antmicro/modular-agilex5e-dc-scm/bios.kicad_sch

## KiCad design bios.kicad_sch (2026-10-01, an earlier design)

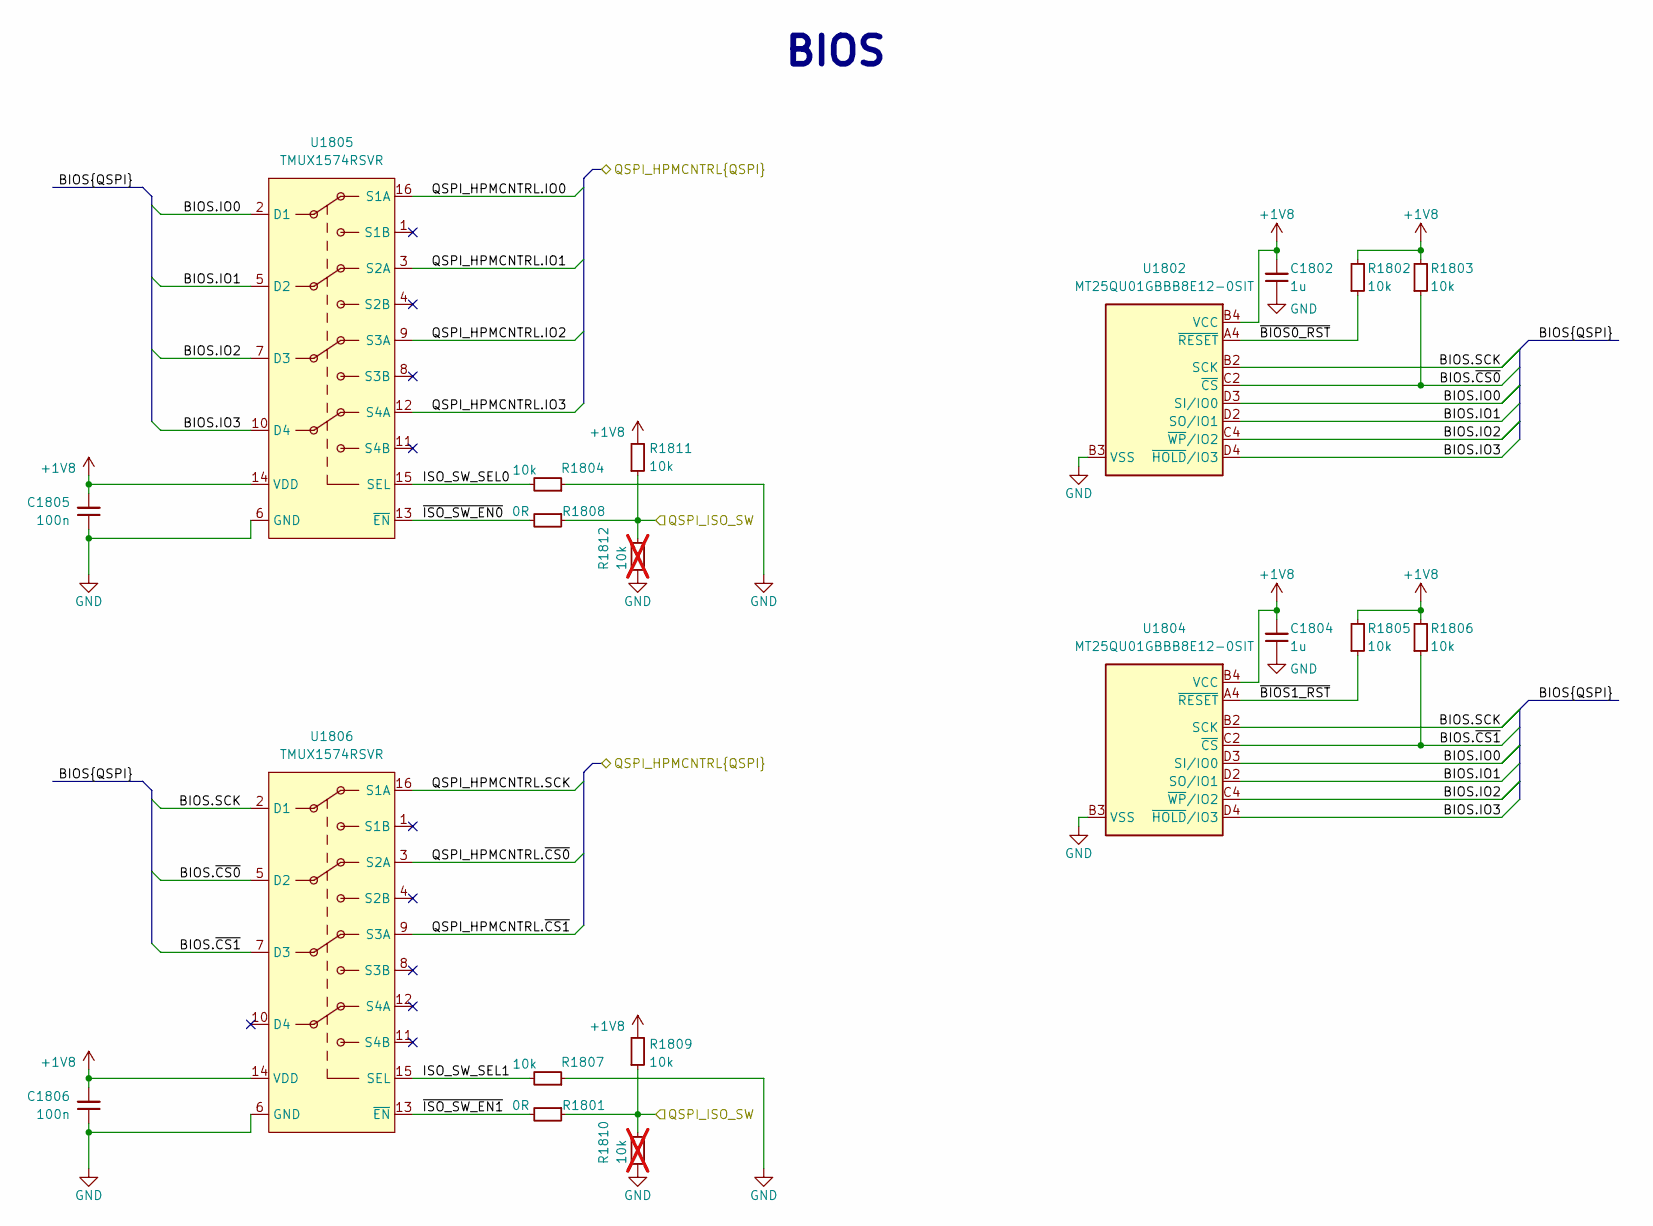
[picture p2: schematic bios.kicad_sch]

Parts:
C1802, C1804: C_1u_0402; C_0402_1005Metric; Voltage 16V; MPN C1005X6S1A105K050BC
C1805, C1806: C_100n_0402; C_0402_1005Metric; Voltage 50V; MPN GRM155R61H104KE14D
R1801, R1808: R_0R_0402; R_0402_1005Metric; MPN ERJ2GE0R00X
R1802, R1803, R1804, R1805, R1806, R1807, R1809, R1811: R_10k_0402; R_0402_1005Metric; Tolerance 1%; MPN CR0402-FX-1002GLF
R1810, R1812: R_10k_0402; R_0402_1005Metric; Tolerance 1%; MPN CR0402-FX-1002GLF; not fitted
U1802, U1804: MT25QU01GBBB8_T-PBGA-24; BGA-25-24_6x8mm_Layout5x5_P1x1mm; MPN MT25QU01GBBB8E12-0SIT
U1805, U1806: TMUX1574RSVR; UQFN-16-1.8x2.6mm_P0.4mm_Texas_RSV0016A; MPN TMUX1574RSVR

Connections:
+1V8: C1802.2, C1804.2, C1805.2, C1806.2, R1802.2, R1803.2, R1805.2, R1806.2, R1809.2, R1811.2, U1802.B4 (VCC), U1804.B4 (VCC), U1805.14 (VDD), U1806.14 (VDD)
BIOS.IO0: U1802.D3 (SI/IO0), U1804.D3 (SI/IO0), U1805.2 (D1)
BIOS.IO1: U1802.D2 (SO/IO1), U1804.D2 (SO/IO1), U1805.5 (D2)
BIOS.IO2: U1802.C4 (~WP/IO2), U1804.C4 (~WP/IO2), U1805.7 (D3)
BIOS.IO3: U1802.D4 (~HOLD/IO3), U1804.D4 (~HOLD/IO3), U1805.10 (D4)
BIOS.SCK: U1802.B2 (SCK), U1804.B2 (SCK), U1806.2 (D1)
BIOS.~CS0: R1803.1, U1802.C2 (~CS), U1806.5 (D2)
BIOS.~CS1: R1806.1, U1804.C2 (~CS), U1806.7 (D3)
GND: C1802.1, C1804.1, C1805.1, C1806.1, R1804.1, R1807.1, R1810.2, R1812.2, U1802.B3 (VSS), U1804.B3 (VSS), U1805.6 (GND), U1806.6 (GND)
ISO_SW_SEL0: R1804.2, U1805.15 (SEL)
ISO_SW_SEL1: R1807.2, U1806.15 (SEL)
unnamed: U1802.A3 (RFU), U1802.A5 (RFU), U1802.B1 (RFU), U1802.B5 (RFU), U1802.C1 (RFU), U1802.C3 (RFU), U1802.C5 (RFU), U1802.D1 (RFU), U1802.D5 (RFU), U1802.E1 (RFU), U1802.E2 (RFU), U1802.E3 (RFU), U1802.E4 (RFU), U1802.E5 (RFU)
unnamed: U1804.A3 (RFU), U1804.A5 (RFU), U1804.B1 (RFU), U1804.B5 (RFU), U1804.C1 (RFU), U1804.C3 (RFU), U1804.C5 (RFU), U1804.D1 (RFU), U1804.D5 (RFU), U1804.E1 (RFU), U1804.E2 (RFU), U1804.E3 (RFU), U1804.E4 (RFU), U1804.E5 (RFU)
QSPI_HPMCNTRL.IO0: U1805.16 (S1A)
QSPI_HPMCNTRL.IO1: U1805.3 (S2A)
QSPI_HPMCNTRL.IO2: U1805.9 (S3A)
QSPI_HPMCNTRL.IO3: U1805.12 (S4A)
QSPI_HPMCNTRL.SCK: U1806.16 (S1A)
QSPI_HPMCNTRL.~CS0: U1806.3 (S2A)
QSPI_HPMCNTRL.~CS1: U1806.9 (S3A)
QSPI_ISO_SW: R1801.1, R1808.1, R1809.1, R1810.1, R1811.1, R1812.1
~BIOS0_RST: R1802.1, U1802.A4 (~RESET)
~BIOS1_RST: R1805.1, U1804.A4 (~RESET)
~ISO_SW_EN0: R1808.2, U1805.13 (~EN)
~ISO_SW_EN1: R1801.2, U1806.13 (~EN)

Notes on the sheet:
BIOS
