antmicro/modular-agilex5e-dc-scm/clk.kicad_sch

## KiCad design clk.kicad_sch (2026-10-01, an earlier design)

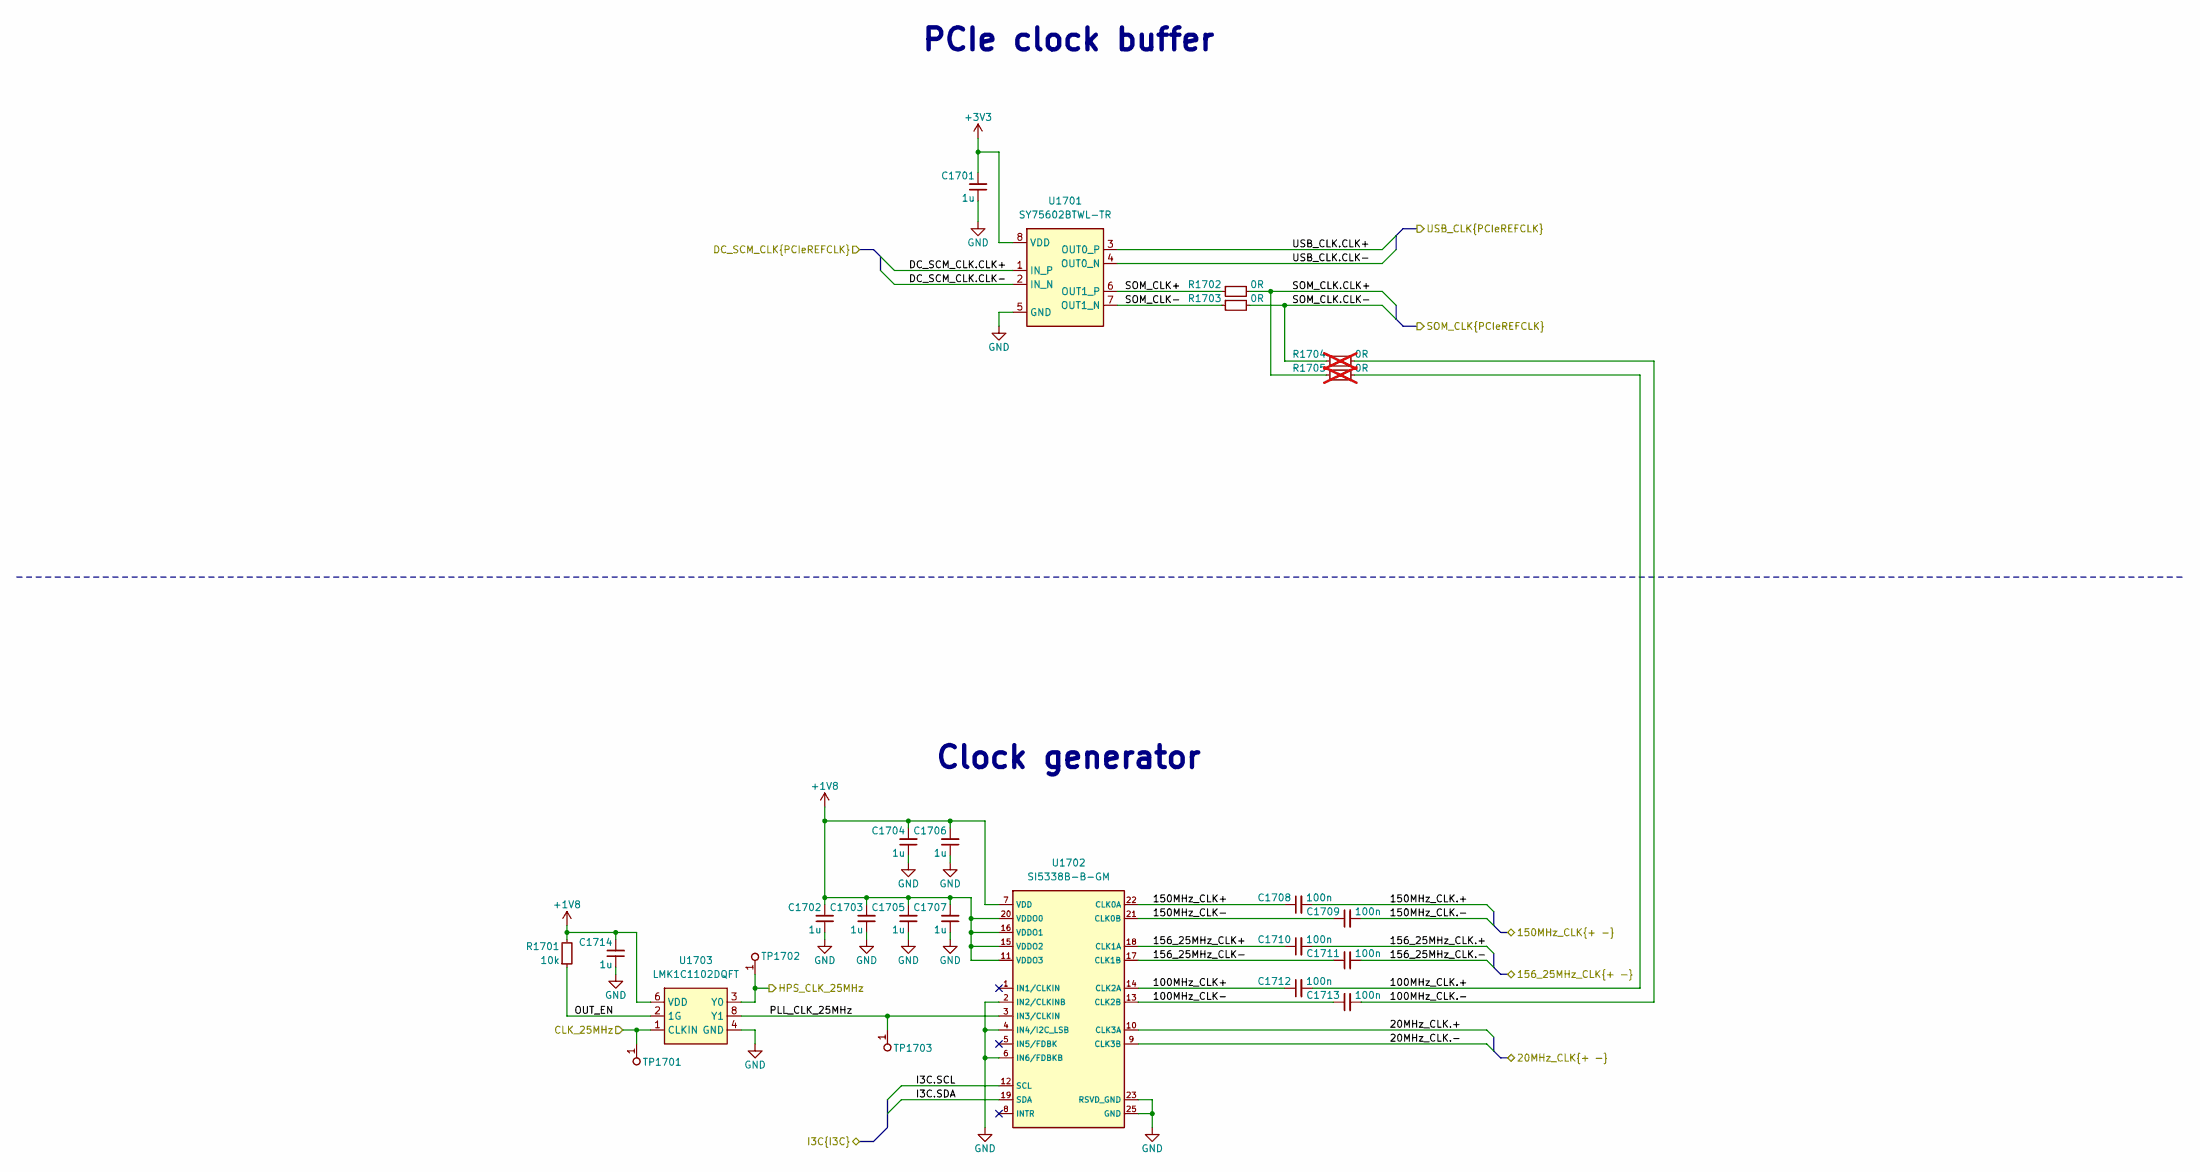
[picture p3: schematic clk.kicad_sch]

Parts:
C1701, C1702, C1703, C1704, C1705, C1706, C1707, C1714: C_1u_0402; C_0402_1005Metric; MPN C1005X6S1A105K050BC
C1708, C1709, C1710, C1711, C1712, C1713: C_100n_0402; C_0402_1005Metric; Voltage 50V; MPN GRM155R61H104KE14D
R1701: R_10k_0402; R_0402_1005Metric; Tolerance 1%; MPN CR0402-FX-1002GLF
R1702, R1703: R_0R_0402; R_0402_1005Metric; MPN ERJ2GE0R00X
R1704, R1705: R_0R_0402; R_0402_1005Metric; MPN ERJ2GE0R00X; not fitted
TP1701, TP1702, TP1703: TP_0.75mm_SMD; TP_SMD_0.75mm
U1701: SY75602BTWL-TR; VDFN-8_1.6x1.4mm_P0.4mm; MPN SY75602BTWL-TR
U1702: SI5338B-B-GM; QFN-24-1EP_4x4mm_P0.5_EP2.5x2.5mm; MPN SI5338B-B-GM
U1703: LMK1C1102DQFT; WSON-8_2x2mm; MPN LMK1C1102DQFT

Connections:
20MHz_CLK.+: U1702.10 (CLK3A)
20MHz_CLK.-: U1702.9 (CLK3B)
100MHz_CLK+: C1712.1, U1702.14 (CLK2A)
100MHz_CLK-: C1713.1, U1702.13 (CLK2B)
100MHz_CLK.+: C1712.2, R1705.2
100MHz_CLK.-: C1713.2, R1704.2
150MHz_CLK+: C1708.1, U1702.22 (CLK0A)
150MHz_CLK-: C1709.1, U1702.21 (CLK0B)
150MHz_CLK.+: C1708.2
150MHz_CLK.-: C1709.2
156_25MHz_CLK+: C1710.1, U1702.18 (CLK1A)
156_25MHz_CLK-: C1711.1, U1702.17 (CLK1B)
156_25MHz_CLK.+: C1710.2
156_25MHz_CLK.-: C1711.2
+1V8: C1702.2, C1703.2, C1704.2, C1705.2, C1706.2, C1707.2, C1714.2, R1701.2, U1702.7 (VDD), U1702.11 (VDDO3), U1702.15 (VDDO2), U1702.16 (VDDO1), U1702.20 (VDDO0), U1702.24 (VDD), U1703.6 (VDD)
+3V3: C1701.2, U1701.8 (VDD)
CLK_25MHz: TP1701.1, U1703.1 (CLKIN)
DC_SCM_CLK.CLK+: U1701.1 (IN_P)
DC_SCM_CLK.CLK-: U1701.2 (IN_N)
GND: C1701.1, C1702.1, C1703.1, C1704.1, C1705.1, C1706.1, C1707.1, C1714.1, U1701.5 (GND), U1702.2 (IN2/CLKINB), U1702.4 (IN4/I2C_LSB), U1702.6 (IN6/FDBKB), U1702.23 (RSVD_GND), U1702.25 (GND), U1703.4 (GND)
HPS_CLK_25MHz: TP1702.1, U1703.3 (Y0)
I3C.SCL: U1702.12 (SCL)
I3C.SDA: U1702.19 (SDA)
OUT_EN: R1701.1, U1703.2 (1G)
PLL_CLK_25MHz: TP1703.1, U1702.3 (IN3/CLKIN), U1703.8 (Y1)
SOM_CLK+: R1702.1, U1701.6 (OUT1_P)
SOM_CLK-: R1703.1, U1701.7 (OUT1_N)
SOM_CLK.CLK+: R1702.2, R1705.1
SOM_CLK.CLK-: R1703.2, R1704.1
USB_CLK.CLK+: U1701.3 (OUT0_P)
USB_CLK.CLK-: U1701.4 (OUT0_N)

Notes on the sheet:
PCIe clock buffer
Clock generator
