antmicro/modular-agilex5e-dc-scm/ftdi.kicad_sch

## KiCad design ftdi.kicad_sch (2026-10-01, an earlier design)

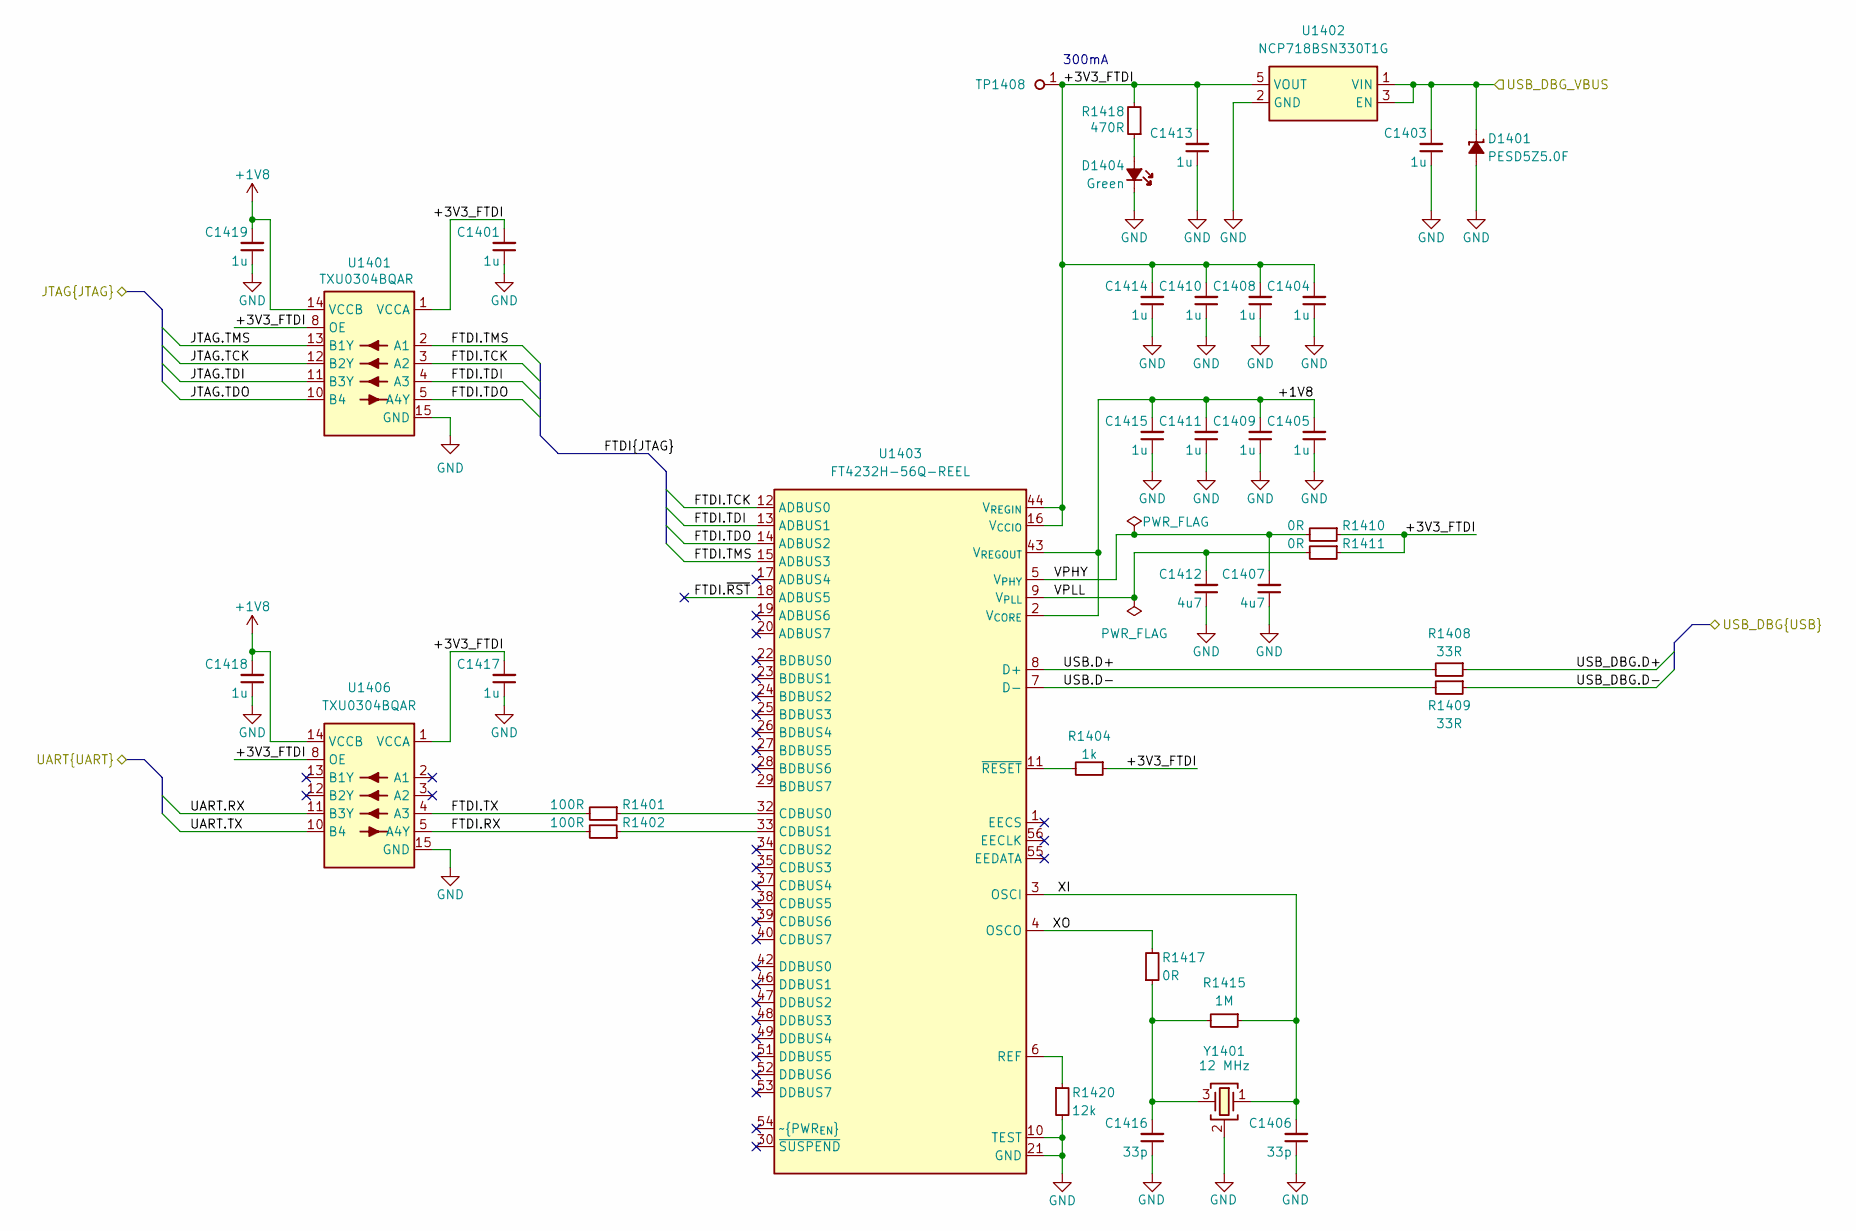
[picture p4: schematic ftdi.kicad_sch]

Parts:
C1401, C1403, C1404, C1405, C1408, C1409, C1410, C1411, C1413, C1414, C1415, C1417, C1418, C1419: C_1u_0402; C_0402_1005Metric; MPN C1005X6S1A105K050BC
C1406, C1416: C_33p_0402; C_0402_1005Metric; MPN 04025A330FAT2A
C1407, C1412: C_4u7_0402; C_0402_1005Metric; MPN GRM155R61A475MEAAD
D1401: PESD5Z5_0F; SOD-523; MPN PESD5Z5.0F
D1404: LED_G_0603_LG_L29K-G2J1-24-Z; LED_0603_1608Metric_G; MPN LG L29K-G2J1-24-Z
R1401, R1402: R_100R_0402; R_0402_1005Metric; Tolerance 1%; MPN CR0402-FX-1000GLF
R1404: R_1k_0402; R_0402_1005Metric; Tolerance 1%; MPN CR0402-FX-1001GLF
R1408, R1409: R_33R_0402; R_0402_1005Metric; Tolerance 1%; MPN CR0402-FX-33R0GLF
R1410, R1411, R1417: R_0R_0402; R_0402_1005Metric; MPN ERJ2GE0R00X
R1415: R_1M_0402; R_0402_1005Metric; Tolerance 1%; MPN CR0402-FX-1004GLF
R1418: R_470R_0402; R_0402_1005Metric; Tolerance 1%; MPN CR0402-FX-4700GLF
R1420: R_12k_0402; R_0402_1005Metric; Tolerance 1%; MPN CR0402-FX-1202GLF
TP1408: TP_1mm_SMD; TP_SMD_1mm
U1401, U1406: TXU0204BQAR; DHVQFN-14-1EP_2.5x3mm; MPN TXU0304BQAR
U1402: NCP718BSN330T1G; SOT-23-5; MPN NCP718BSN330T1G
U1403: FT4232H_VQFN; QFN-56-1EP_8x8mm_P0.5mm; MPN FT4232H-56Q-REEL
Y1401: Resonator_12MHz_ABM8G; Resonator_SMD_Abracon_ABM8G_3.2x2.5mm; MPN ABM8G-12.000MHZ-18-D2Y-T

Connections:
+1V8: C1405.2, C1409.2, C1411.2, C1415.2, C1418.2, C1419.2, U1401.14 (VCCB), U1403.2 (V_{CORE}), U1403.31 (V_{CORE}), U1403.43 (V_{REGOUT}), U1406.14 (VCCB)
+3V3_FTDI: C1401.2, C1404.2, C1408.2, C1410.2, C1413.2, C1414.2, C1417.2, R1404.1, R1410.1, R1411.1, R1418.2, TP1408.1, U1401.1 (VCCA), U1401.8 (OE), U1402.5 (VOUT), U1403.16 (V_{CCIO}), U1403.36 (V_{CCIO}), U1403.44 (V_{REGIN}), U1403.50 (V_{CCIO}), U1406.1 (VCCA), U1406.8 (OE)
FTDI.RX: R1402.2, U1406.5 (A4Y)
FTDI.TCK: U1401.3 (A2), U1403.12 (ADBUS0)
FTDI.TDI: U1401.4 (A3), U1403.13 (ADBUS1)
FTDI.TDO: U1401.5 (A4Y), U1403.14 (ADBUS2)
FTDI.TMS: U1401.2 (A1), U1403.15 (ADBUS3)
FTDI.TX: R1401.2, U1406.4 (A3)
FTDI.~RST: U1403.18 (ADBUS5)
GND: C1401.1, C1403.1, C1404.1, C1405.1, C1406.1, C1407.1, C1408.1, C1409.1, C1410.1, C1411.1, C1412.1, C1413.1, C1414.1, C1415.1, C1416.1, C1417.1, C1418.1, C1419.1, D1401.2 (A), D1404.1 (C), R1420.2, U1401.7 (GND), U1401.15 (GND), U1402.2 (GND), U1403.10 (TEST), U1403.21 (GND), U1403.41 (GND), U1403.45 (GND), U1403.57 (GND), U1406.7 (GND), U1406.15 (GND), Y1401.2 (SH), Y1401.4 (SH)
JTAG.TCK: U1401.12 (B2Y)
JTAG.TDI: U1401.11 (B3Y)
JTAG.TDO: U1401.10 (B4)
JTAG.TMS: U1401.13 (B1Y)
unnamed: C1416.2, R1415.2, R1417.1, Y1401.3
unnamed: D1404.2 (A), R1418.1
unnamed: R1401.1, U1403.32 (CDBUS0)
unnamed: R1402.1, U1403.33 (CDBUS1)
unnamed: R1404.2, U1403.11 (~RESET)
unnamed: R1420.1, U1403.6 (REF)
UART.RX: U1406.11 (B3Y)
UART.TX: U1406.10 (B4)
USB.D+: R1408.2, U1403.8 (D+)
USB.D-: R1409.2, U1403.7 (D-)
USB_DBG.D+: R1408.1
USB_DBG.D-: R1409.1
USB_DBG_VBUS: C1403.2, D1401.1 (C), U1402.1 (VIN), U1402.3 (EN)
VPHY: C1407.2, R1410.2, U1403.5 (V_{PHY})
VPLL: C1412.2, R1411.2, U1403.9 (V_{PLL})
XI: C1406.2, R1415.1, U1403.3 (OSCI), Y1401.1
XO: R1417.2, U1403.4 (OSCO)

Notes on the sheet:
300mA
