antmicro/modular-agilex5e-dc-scm/ltpi_bias.kicad_sch

## KiCad design ltpi_bias.kicad_sch (2026-10-01, an earlier design)

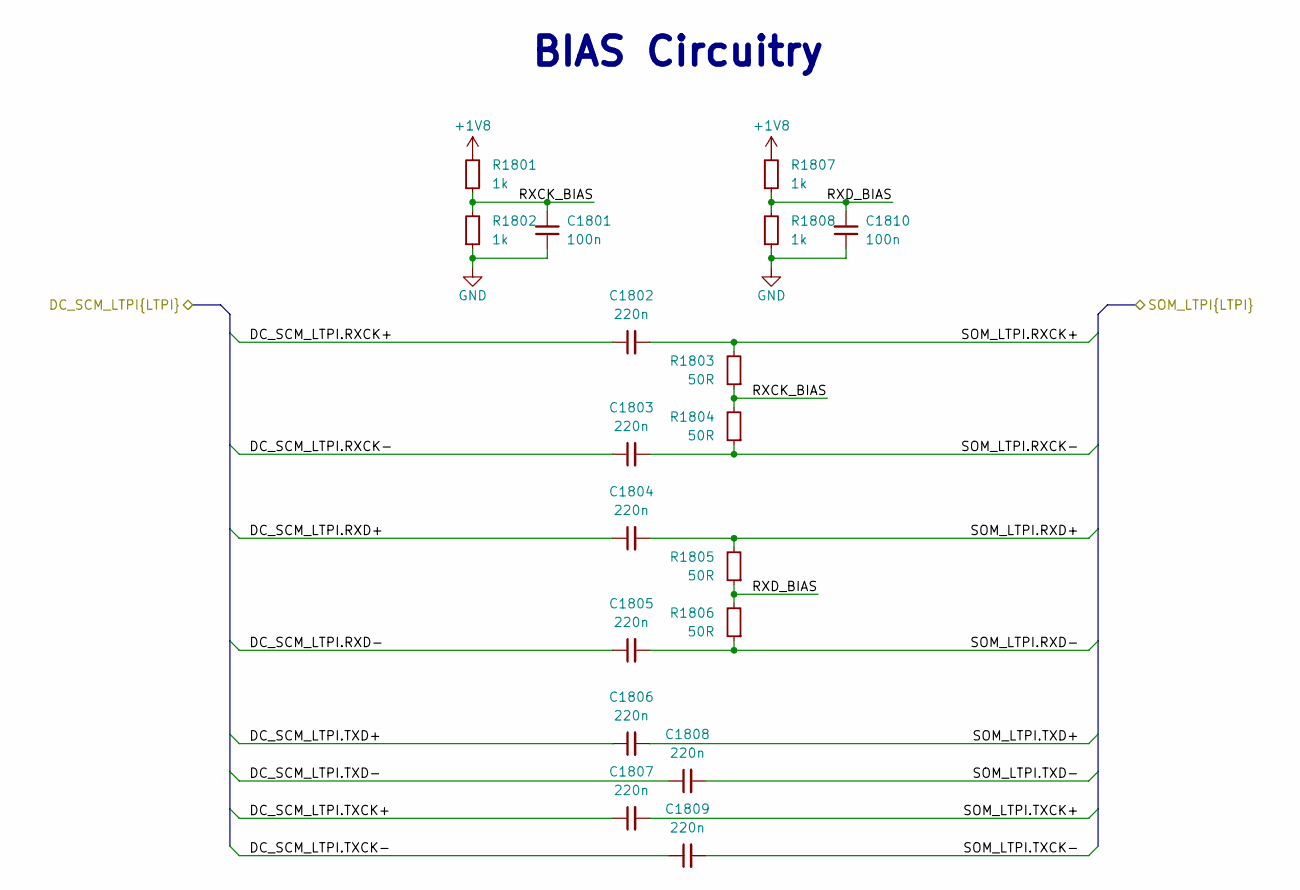
[picture p5: schematic ltpi_bias.kicad_sch]

Parts:
C1801, C1810: C_100n_16V_X7R_0402; C_0402_1005Metric; Voltage 16V; MPN C0402C104J4RAC7411
C1802, C1803, C1804, C1805, C1806, C1807, C1808, C1809: C_220n_6V3_X7R_0402; C_0402_1005Metric; Voltage 6.3V; MPN C0402C224M9RACTU
R1801, R1802, R1807, R1808: R_1k_0402; R_0402_1005Metric; Tolerance 1%; MPN CR0402-FX-1001GLF
R1803, R1804, R1805, R1806: R_50R_0402; R_0402_1005Metric; Tolerance 1%; MPN CR0402-FX-50R0GLF

Connections:
+1V8: R1801.2, R1807.2
DC_SCM_LTPI.RXCK+: C1802.1
DC_SCM_LTPI.RXCK-: C1803.1
DC_SCM_LTPI.RXD+: C1804.1
DC_SCM_LTPI.RXD-: C1805.1
DC_SCM_LTPI.TXCK+: C1807.1
DC_SCM_LTPI.TXCK-: C1809.1
DC_SCM_LTPI.TXD+: C1806.1
DC_SCM_LTPI.TXD-: C1808.1
GND: C1801.1, C1810.1, R1802.1, R1808.1
RXCK_BIAS: C1801.2, R1801.1, R1802.2, R1803.1, R1804.2
RXD_BIAS: C1810.2, R1805.1, R1806.2, R1807.1, R1808.2
SOM_LTPI.RXCK+: C1802.2, R1803.2
SOM_LTPI.RXCK-: C1803.2, R1804.1
SOM_LTPI.RXD+: C1804.2, R1805.2
SOM_LTPI.RXD-: C1805.2, R1806.1
SOM_LTPI.TXCK+: C1807.2
SOM_LTPI.TXCK-: C1809.2
SOM_LTPI.TXD+: C1806.2
SOM_LTPI.TXD-: C1808.2

Notes on the sheet:
BIAS Circuitry
