antmicro/modular-agilex5e-dc-scm/misc.kicad_sch

## KiCad design misc.kicad_sch (2026-10-01, an earlier design)

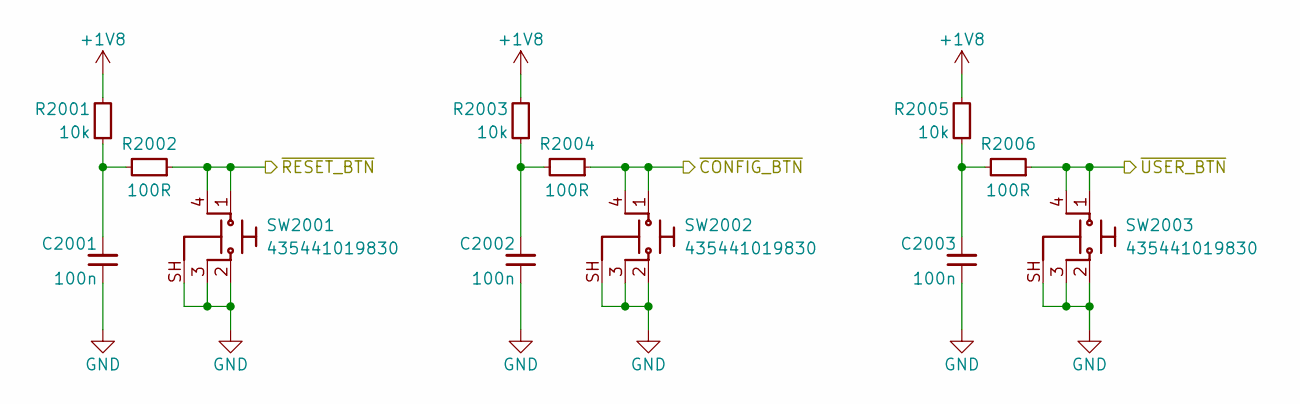
[picture p6: schematic misc.kicad_sch]

Parts:
C2001, C2002, C2003: C_100n_0402; C_0402_1005Metric; Voltage 50V; MPN GRM155R61H104KE14D
R2001, R2003, R2005: R_10k_0402; R_0402_1005Metric; Tolerance 1%; MPN CR0402-FX-1002GLF
R2002, R2004, R2006: R_100R_0402; R_0402_1005Metric; Tolerance 1%; MPN CR0402-FX-1000GLF
SW2001, SW2002, SW2003: SW_435441019830_SMD; MPN 435441019830

Connections:
+1V8: R2001.2, R2003.2, R2005.2
GND: C2001.1, C2002.1, C2003.1, SW2001.2, SW2001.3, SW2001.SH, SW2002.2, SW2002.3, SW2002.SH, SW2003.2, SW2003.3, SW2003.SH
unnamed: C2001.2, R2001.1, R2002.2
unnamed: C2002.2, R2003.1, R2004.2
unnamed: C2003.2, R2005.1, R2006.2
~CONFIG_BTN: R2004.1, SW2002.1, SW2002.4
~RESET_BTN: R2002.1, SW2001.1, SW2001.4
~USER_BTN: R2006.1, SW2003.1, SW2003.4
