antmicro/modular-agilex5e-dc-scm/mitysom-hps.kicad_sch

## KiCad design mitysom-hps.kicad_sch (2026-10-01, an earlier design)

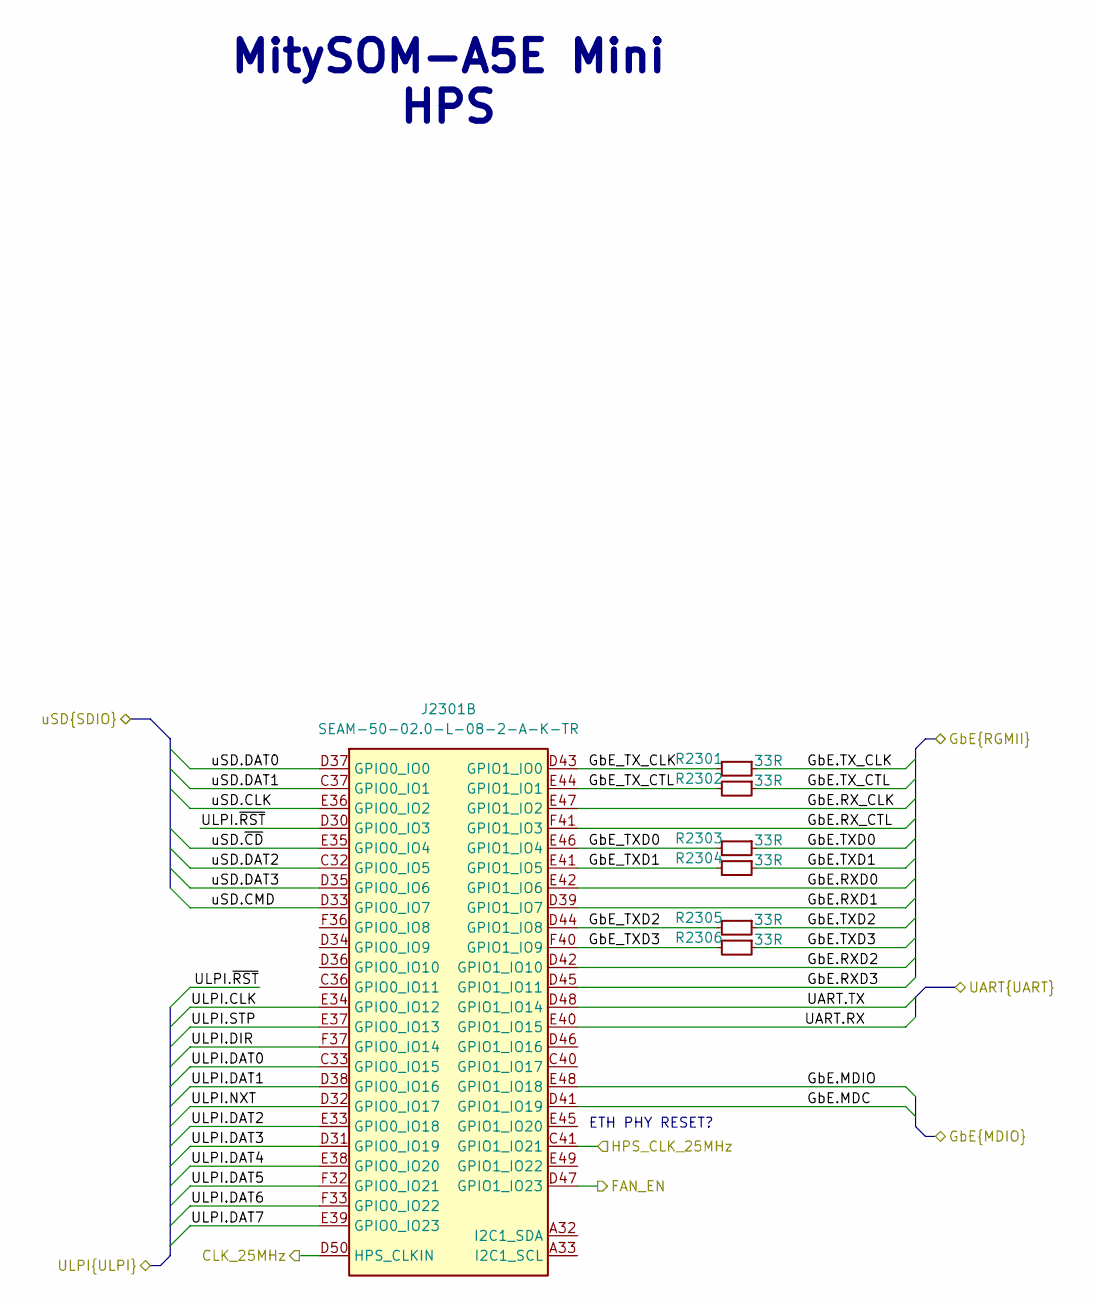
[picture p7: schematic mitysom-hps.kicad_sch]

Parts:
J2301: Plug_Samtec_SEAM-50-02.0-L-08-2-A-K-TR_CUSTOM_Mit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; Conn_Plug_Samtec_SEAM-50-02.0-S-08-2-A-K-TR; MPN SEAM-50-02.0-L-08-2-A-K-TR
R2301, R2302, R2303, R2304, R2305, R2306: R_33R_0402; R_0402_1005Metric; Tolerance 1%; MPN CR0402-FX-33R0GLF

Connections:
CLK_25MHz: J2301.D50 (HPS_CLKIN)
FAN_EN: J2301.D47 (GPIO1_IO23)
GbE.MDC: J2301.D41 (GPIO1_IO19)
GbE.MDIO: J2301.E48 (GPIO1_IO18)
GbE.RXD0: J2301.E42 (GPIO1_IO6)
GbE.RXD1: J2301.D39 (GPIO1_IO7)
GbE.RXD2: J2301.D42 (GPIO1_IO10)
GbE.RXD3: J2301.D45 (GPIO1_IO11)
GbE.RX_CLK: J2301.E47 (GPIO1_IO2)
GbE.RX_CTL: J2301.F41 (GPIO1_IO3)
GbE.TXD0: R2303.1
GbE.TXD1: R2304.1
GbE.TXD2: R2305.1
GbE.TXD3: R2306.1
GbE.TX_CLK: R2301.1
GbE.TX_CTL: R2302.1
GbE_TXD0: J2301.E46 (GPIO1_IO4), R2303.2
GbE_TXD1: J2301.E41 (GPIO1_IO5), R2304.2
GbE_TXD2: J2301.D44 (GPIO1_IO8), R2305.2
GbE_TXD3: J2301.F40 (GPIO1_IO9), R2306.2
GbE_TX_CLK: J2301.D43 (GPIO1_IO0), R2301.2
GbE_TX_CTL: J2301.E44 (GPIO1_IO1), R2302.2
HPS_CLK_25MHz: J2301.C41 (GPIO1_IO21)
UART.RX: J2301.E40 (GPIO1_IO15)
UART.TX: J2301.D48 (GPIO1_IO14)
ULPI.CLK: J2301.E34 (GPIO0_IO12)
ULPI.DAT0: J2301.C33 (GPIO0_IO15)
ULPI.DAT1: J2301.D38 (GPIO0_IO16)
ULPI.DAT2: J2301.E33 (GPIO0_IO18)
ULPI.DAT3: J2301.D31 (GPIO0_IO19)
ULPI.DAT4: J2301.E38 (GPIO0_IO20)
ULPI.DAT5: J2301.F32 (GPIO0_IO21)
ULPI.DAT6: J2301.F33 (GPIO0_IO22)
ULPI.DAT7: J2301.E39 (GPIO0_IO23)
ULPI.DIR: J2301.F37 (GPIO0_IO14)
ULPI.NXT: J2301.D32 (GPIO0_IO17)
ULPI.STP: J2301.E37 (GPIO0_IO13)
ULPI.~RST: J2301.D30 (GPIO0_IO3)
uSD.CLK: J2301.E36 (GPIO0_IO2)
uSD.CMD: J2301.D33 (GPIO0_IO7)
uSD.DAT0: J2301.D37 (GPIO0_IO0)
uSD.DAT1: J2301.C37 (GPIO0_IO1)
uSD.DAT2: J2301.C32 (GPIO0_IO5)
uSD.DAT3: J2301.D35 (GPIO0_IO6)
uSD.~CD: J2301.E35 (GPIO0_IO4)

Notes on the sheet:
MitySOM-A5E Mini HPS
ETH PHY RESET?
