antmicro/modular-agilex5e-dc-scm/mitysom-hsio.kicad_sch

## KiCad design mitysom-hsio.kicad_sch (2026-10-01, an earlier design)

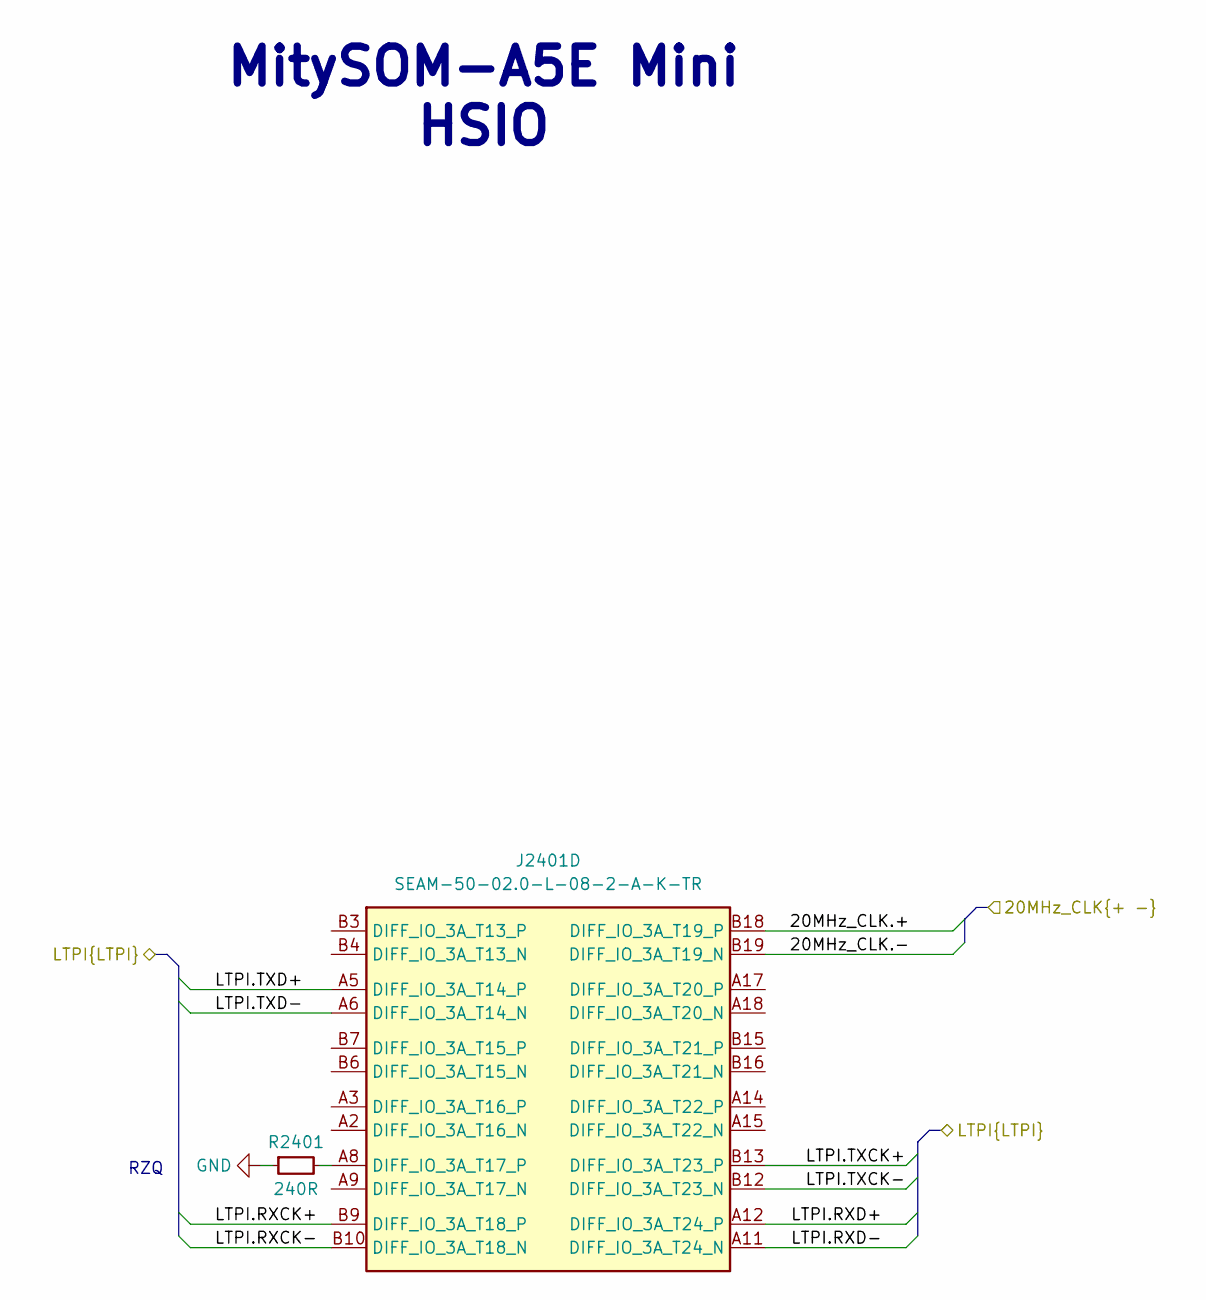
[picture p8: schematic mitysom-hsio.kicad_sch]

Parts:
J2401: Plug_Samtec_SEAM-50-02.0-L-08-2-A-K-TR_CUSTOM_Mit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; Conn_Plug_Samtec_SEAM-50-02.0-S-08-2-A-K-TR; MPN SEAM-50-02.0-L-08-2-A-K-TR
R2401: R_240R_0402; R_0402_1005Metric; Tolerance 1%; MPN CR0402-FX-2400GLF

Connections:
20MHz_CLK.+: J2401.B18 (DIFF_IO_3A_T19_P)
20MHz_CLK.-: J2401.B19 (DIFF_IO_3A_T19_N)
GND: R2401.1
LTPI.RXCK+: J2401.B9 (DIFF_IO_3A_T18_P)
LTPI.RXCK-: J2401.B10 (DIFF_IO_3A_T18_N)
LTPI.RXD+: J2401.A12 (DIFF_IO_3A_T24_P)
LTPI.RXD-: J2401.A11 (DIFF_IO_3A_T24_N)
LTPI.TXCK+: J2401.B13 (DIFF_IO_3A_T23_P)
LTPI.TXCK-: J2401.B12 (DIFF_IO_3A_T23_N)
LTPI.TXD+: J2401.A5 (DIFF_IO_3A_T14_P)
LTPI.TXD-: J2401.A6 (DIFF_IO_3A_T14_N)
unnamed: J2401.A8 (DIFF_IO_3A_T17_P), R2401.2

Notes on the sheet:
RZQ
MitySOM-A5E Mini HSIO
