antmicro/modular-agilex5e-dc-scm/mitysom-power.kicad_sch

## KiCad design mitysom-power.kicad_sch (2026-10-01, an earlier design)

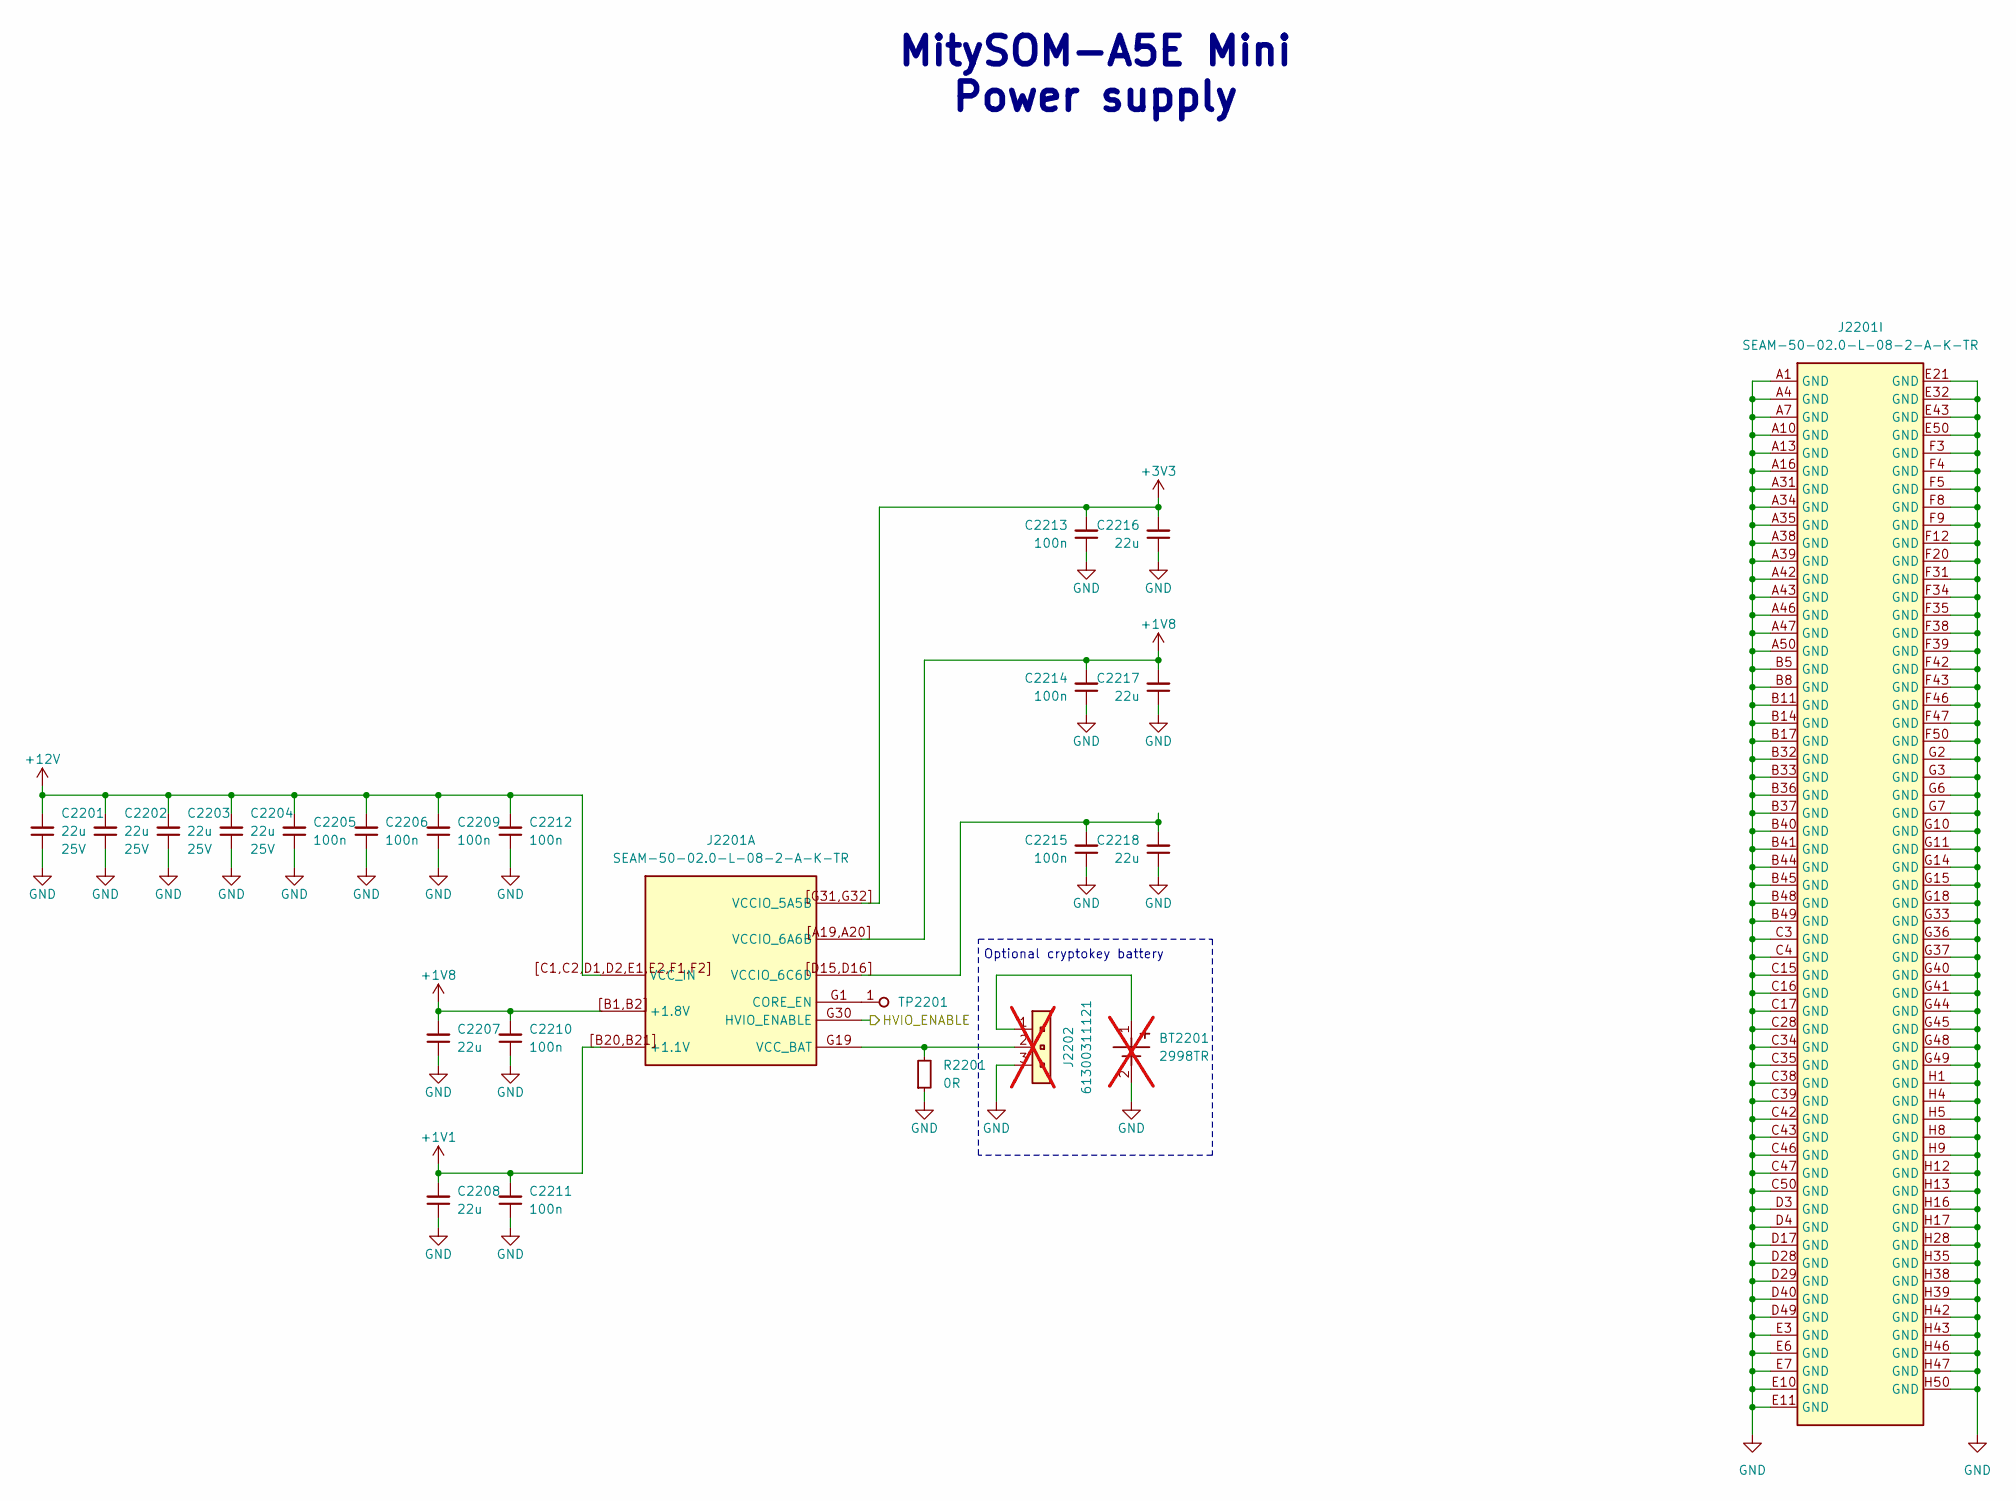
[picture p9: schematic mitysom-power.kicad_sch]

Parts:
BT2201: Battery_Holder_2998TR; MPN 2998TR; not fitted
C2201, C2202, C2203, C2204: C_22u_25V_0805; C_0805_2012Metric; Voltage 25V; MPN CL21A226MAYNNNE
C2205, C2206, C2209, C2210, C2211, C2212, C2213, C2214, C2215: C_100n_0402; C_0402_1005Metric; Voltage 50V; MPN GRM155R61H104KE14D
C2207, C2208, C2216, C2217, C2218: C_22u_10V_0402; C_0402_1005Metric; Voltage 10V; MPN GRM158R61A226ME15D
J2201: Plug_Samtec_SEAM-50-02.0-L-08-2-A-K-TR_CUSTOM_Mit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; Conn_Plug_Samtec_SEAM-50-02.0-S-08-2-A-K-TR; MPN SEAM-50-02.0-L-08-2-A-K-TR
J2202: PinHeader_1x3_P2.54mm_Drill1.1mm; MPN 61300311121; not fitted
R2201: R_0R_0402; R_0402_1005Metric; MPN ERJ2GE0R00X
TP2201: TP_1mm_SMD; TP_SMD_1mm

Connections:
+1V1: C2208.2, C2211.2, J2201.[B20,B21] (+1.1V)
+1V8: C2207.2, C2210.2, C2214.2, C2217.2, J2201.[A19,A20] (VCCIO_6A6B), J2201.[B1,B2] (+1.8V)
+3V3: C2213.2, C2216.2, J2201.[G31,G32] (VCCIO_5A5B)
+12V: C2201.2, C2202.2, C2203.2, C2204.2, C2205.2, C2206.2, C2209.2, C2212.2, J2201.[C1,C2,D1,D2,E1,E2,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 (VCC_IN)
GND: BT2201.2 (GND), C2201.1, C2202.1, C2203.1, C2204.1, C2205.1, C2206.1, C2207.1, C2208.1, C2209.1, C2210.1, C2211.1, C2212.1, C2213.1, C2214.1, C2215.1, C2216.1, C2217.1, C2218.1, J2201.A1 (GND), J2201.A4 (GND), J2201.A7 (GND), J2201.A10 (GND), J2201.A13 (GND), J2201.A16 (GND), J2201.A31 (GND), J2201.A34 (GND), J2201.A35 (GND), J2201.A38 (GND), J2201.A39 (GND), J2201.A42 (GND), J2201.A43 (GND), J2201.A46 (GND), J2201.A47 (GND), J2201.A50 (GND), J2201.B5 (GND), J2201.B8 (GND), J2201.B11 (GND), J2201.B14 (GND), J2201.B17 (GND), J2201.B32 (GND), J2201.B33 (GND), J2201.B36 (GND), J2201.B37 (GND), J2201.B40 (GND), J2201.B41 (GND), J2201.B44 (GND), J2201.B45 (GND), J2201.B48 (GND), J2201.B49 (GND), J2201.C3 (GND), J2201.C4 (GND), J2201.C15 (GND), J2201.C16 (GND), J2201.C17 (GND), J2201.C28 (GND), J2201.C34 (GND), J2201.C35 (GND), J2201.C38 (GND), J2201.C39 (GND), J2201.C42 (GND), J2201.C43 (GND), J2201.C46 (GND), J2201.C47 (GND), J2201.C50 (GND), J2201.D3 (GND), J2201.D4 (GND), J2201.D17 (GND), J2201.D28 (GND), J2201.D29 (GND), J2201.D40 (GND), J2201.D49 (GND), J2201.E3 (GND), J2201.E6 (GND), J2201.E7 (GND), J2201.E10 (GND), J2201.E11 (GND), J2201.E21 (GND), J2201.E32 (GND), J2201.E43 (GND), J2201.E50 (GND), J2201.F3 (GND), J2201.F4 (GND), J2201.F5 (GND), J2201.F8 (GND), J2201.F9 (GND), J2201.F12 (GND), J2201.F20 (GND), J2201.F31 (GND), J2201.F34 (GND), J2201.F35 (GND), J2201.F38 (GND), J2201.F39 (GND), J2201.F42 (GND), J2201.F43 (GND), J2201.F46 (GND), J2201.F47 (GND), J2201.F50 (GND), J2201.G2 (GND), J2201.G3 (GND), J2201.G6 (GND), J2201.G7 (GND), J2201.G10 (GND), J2201.G11 (GND), J2201.G14 (GND), J2201.G15 (GND), J2201.G18 (GND), J2201.G33 (GND), J2201.G36 (GND), J2201.G37 (GND), J2201.G40 (GND), J2201.G41 (GND), J2201.G44 (GND), J2201.G45 (GND), J2201.G48 (GND), J2201.G49 (GND), J2201.H1 (GND), J2201.H4 (GND), J2201.H5 (GND), J2201.H8 (GND), J2201.H9 (GND), J2201.H12 (GND), J2201.H13 (GND), J2201.H16 (GND), J2201.H17 (GND), J2201.H28 (GND), J2201.H35 (GND), J2201.H38 (GND), J2201.H39 (GND), J2201.H42 (GND), J2201.H43 (GND), J2201.H46 (GND), J2201.H47 (GND), J2201.H50 (GND), J2202.3, R2201.1
HVIO_ENABLE: J2201.G30 (HVIO_ENABLE)
unnamed: BT2201.1 (V_BAT), J2202.1
unnamed: C2215.2, C2218.2, J2201.[D15,D16] (VCCIO_6C6D)
unnamed: J2201.G1 (CORE_EN), TP2201.1
unnamed: J2201.G19 (VCC_BAT), J2202.2, R2201.2

Notes on the sheet:
MitySOM-A5E Mini Power supply
Optional cryptokey battery
